ftobler/inductive_sensor/stm-inductive-sensor/application/stm32_hal.h

/*
 * stm32_hal.h
 *
 *  Created on: Nov 11, 2023
 *      Author: ftobler
 */

#ifndef STM32_HAL_H_
#define STM32_HAL_H_

#include "stm32g0xx.h"
#include "stm32g0xx_hal_def.h"


#endif /* STM32_HAL_H_ */
